Kem4lk/magpanel/hardware/kicad/xlsx.py

# -*- coding: utf-8 -*-
"""
Kucuk XLSX yazici (yalniz stdlib): tek sayfa, ilk satir baslik. Ayni girdi -> ayni dosya (zip tarihi sabit).
Iki gorunum, montaj servislerinin ornek dosyalari gibi:
  varsayilan: Arial 11, lacivert zemin + beyaz kalin baslik, ince kenarlik, baslik sabit (Robotistan)
  plain=True: Calibri 11, bicimsiz (Turkce "default_bomlist" sablonu)
"""
import zipfile
from xml.sax.saxutils import escape

_CT = '''<?xml version="1.0" encoding="UTF-8" standalone="yes"?>
<Types xmlns="http://schemas.openxmlformats.org/package/2006/content-types">
<Default Extension="rels" ContentType="application/vnd.openxmlformats-package.relationships+xml"/>
<Default Extension="xml" ContentType="application/xml"/>
<Override PartName="/xl/workbook.xml" ContentType="application/vnd.openxmlformats-officedocument.spreadsheetml.sheet.main+xml"/>
<Override PartName="/xl/worksheets/sheet1.xml" ContentType="application/vnd.openxmlformats-officedocument.spreadsheetml.worksheet+xml"/>
<Override PartName="/xl/styles.xml" ContentType="application/vnd.openxmlformats-officedocument.spreadsheetml.styles+xml"/>
</Types>'''

_RELS = '''<?xml version="1.0" encoding="UTF-8" standalone="yes"?>
<Relationships xmlns="http://schemas.openxmlformats.org/package/2006/relationships">
<Relationship Id="rId1" Type="http://schemas.openxmlformats.org/officeDocument/2006/relationships/officeDocument" Target="xl/workbook.xml"/>
</Relationships>'''

_WB = '''<?xml version="1.0" encoding="UTF-8" standalone="yes"?>
<workbook xmlns="http://schemas.openxmlformats.org/spreadsheetml/2006/main" xmlns:r="http://schemas.openxmlformats.org/officeDocument/2006/relationships">
<sheets><sheet name="%s" sheetId="1" r:id="rId1"/></sheets>
</workbook>'''

_WB_RELS = '''<?xml version="1.0" encoding="UTF-8" standalone="yes"?>
<Relationships xmlns="http://schemas.openxmlformats.org/package/2006/relationships">
<Relationship Id="rId1" Type="http://schemas.openxmlformats.org/officeDocument/2006/relationships/worksheet" Target="worksheets/sheet1.xml"/>
<Relationship Id="rId2" Type="http://schemas.openxmlformats.org/officeDocument/2006/relationships/styles" Target="styles.xml"/>
</Relationships>'''

# xf 0: varsayilan, xf 1: veri hucresi, xf 2: baslik
_STYLES = '''<?xml version="1.0" encoding="UTF-8" standalone="yes"?>
<styleSheet xmlns="http://schemas.openxmlformats.org/spreadsheetml/2006/main">
<fonts count="3">
<font><sz val="11"/><name val="Arial"/><family val="2"/></font>
<font><sz val="11"/><color rgb="FF172033"/><name val="Arial"/><family val="2"/></font>
<font><b/><sz val="11"/><color rgb="FFFFFFFF"/><name val="Arial"/><family val="2"/></font>
</fonts>
<fills count="3">
<fill><patternFill patternType="none"/></fill>
<fill><patternFill patternType="gray125"/></fill>
<fill><patternFill patternType="solid"><fgColor rgb="FF0B1F3A"/><bgColor indexed="64"/></patternFill></fill>
</fills>
<borders count="2">
<border><left/><right/><top/><bottom/><diagonal/></border>
<border><left style="thin"><color rgb="FFD0D5DD"/></left><right style="thin"><color rgb="FFD0D5DD"/></right><top style="thin"><color rgb="FFD0D5DD"/></top><bottom style="thin"><color rgb="FFD0D5DD"/></bottom><diagonal/></border>
</borders>
<cellStyleXfs count="1"><xf numFmtId="0" fontId="0" fillId="0" borderId="0"/></cellStyleXfs>
<cellXfs count="3">
<xf numFmtId="0" fontId="0" fillId="0" borderId="0" xfId="0"/>
<xf numFmtId="0" fontId="1" fillId="0" borderId="1" xfId="0" applyFont="1" applyBorder="1" applyAlignment="1"><alignment vertical="center"/></xf>
<xf numFmtId="0" fontId="2" fillId="2" borderId="1" xfId="0" applyFont="1" applyFill="1" applyBorder="1" applyAlignment="1"><alignment horizontal="center" vertical="center" wrapText="1"/></xf>
</cellXfs>
<cellStyles count="1"><cellStyle name="Normal" xfId="0" builtinId="0"/></cellStyles>
</styleSheet>'''

_STYLES_PLAIN = '''<?xml version="1.0" encoding="UTF-8" standalone="yes"?>
<styleSheet xmlns="http://schemas.openxmlformats.org/spreadsheetml/2006/main">
<fonts count="1"><font><sz val="11"/><color rgb="FF000000"/><name val="Calibri"/><family val="2"/></font></fonts>
<fills count="2"><fill><patternFill patternType="none"/></fill><fill><patternFill patternType="gray125"/></fill></fills>
<borders count="1"><border><left/><right/><top/><bottom/><diagonal/></border></borders>
<cellStyleXfs count="1"><xf numFmtId="0" fontId="0" fillId="0" borderId="0"/></cellStyleXfs>
<cellXfs count="3">
<xf numFmtId="0" fontId="0" fillId="0" borderId="0" xfId="0"/>
<xf numFmtId="0" fontId="0" fillId="0" borderId="0" xfId="0"/>
<xf numFmtId="0" fontId="0" fillId="0" borderId="0" xfId="0"/>
</cellXfs>
<cellStyles count="1"><cellStyle name="Normal" xfId="0" builtinId="0"/></cellStyles>
</styleSheet>'''


def _col(i):
    """0 -> A, 25 -> Z, 26 -> AA"""
    s = ''
    i += 1
    while i:
        i, r = divmod(i - 1, 26)
        s = chr(65 + r) + s
    return s


def _cell(ref, v, style):
    if isinstance(v, bool) or v is None:
        v = '' if v is None else str(v)
    if isinstance(v, (int, float)):
        return '<c r="%s" s="%d"><v>%s</v></c>' % (ref, style, repr(v))
    return '<c r="%s" s="%d" t="inlineStr"><is><t xml:space="preserve">%s</t></is></c>' % (ref, style, escape(str(v)))


def write(path, rows, widths=None, sheet='Sheet1', header_height=30, plain=False):
    """rows[0] baslik, gerisi veri (str ya da sayi). widths: sutun genislikleri (karakter)."""
    cols = ''
    if widths:
        cols = '<cols>%s</cols>' % ''.join('<col min="%d" max="%d" width="%g" customWidth="1"/>' % (i + 1, i + 1, w)
                                           for i, w in enumerate(widths))
    body = []
    for r, row in enumerate(rows, 1):
        style = 2 if r == 1 else 1
        attrs = ' ht="%g" customHeight="1"' % header_height if r == 1 and not plain else ''
        body.append('<row r="%d"%s>%s</row>' % (r, attrs, ''.join(_cell('%s%d' % (_col(i), r), v, style)
                                                                   for i, v in enumerate(row))))
    ws = ('<?xml version="1.0" encoding="UTF-8" standalone="yes"?>\n'
          '<worksheet xmlns="http://schemas.openxmlformats.org/spreadsheetml/2006/main">%s%s<sheetData>%s</sheetData>'
          '</worksheet>' % ('' if plain else '<sheetViews><sheetView workbookViewId="0"><pane ySplit="1" topLeftCell="A2" '
                            'activePane="bottomLeft" state="frozen"/></sheetView></sheetViews>', cols, ''.join(body)))
    parts = [('[Content_Types].xml', _CT), ('_rels/.rels', _RELS), ('xl/workbook.xml', _WB % escape(sheet)),
             ('xl/_rels/workbook.xml.rels', _WB_RELS), ('xl/styles.xml', _STYLES_PLAIN if plain else _STYLES),
             ('xl/worksheets/sheet1.xml', ws)]
    with zipfile.ZipFile(path, 'w', zipfile.ZIP_DEFLATED) as z:
        for name, data in parts:
            zi = zipfile.ZipInfo(name, date_time=(2026, 1, 1, 0, 0, 0))
            zi.compress_type = zipfile.ZIP_DEFLATED
            z.writestr(zi, data.encode('utf-8'))
